jvonk/MIDImike/media/arduino.Still001.jpg

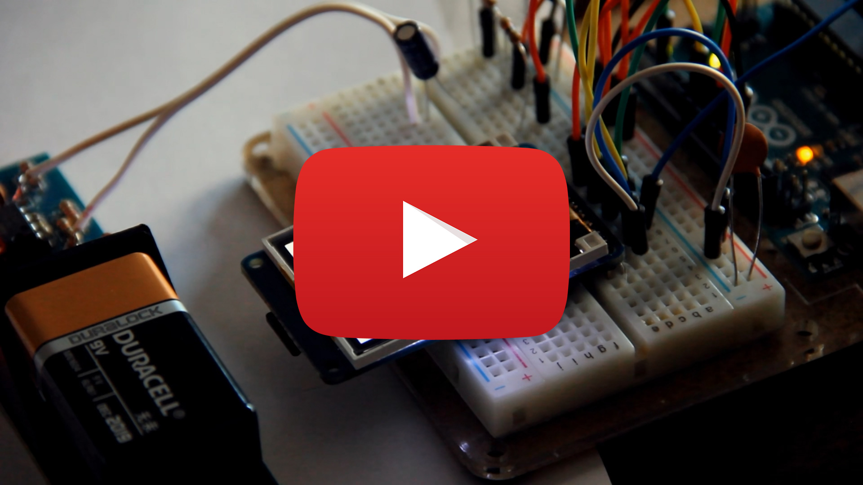
media/arduino.Still001.jpg
