jvonk/MIDImike/validation/N=200, S=9615, piano, interpolation.png

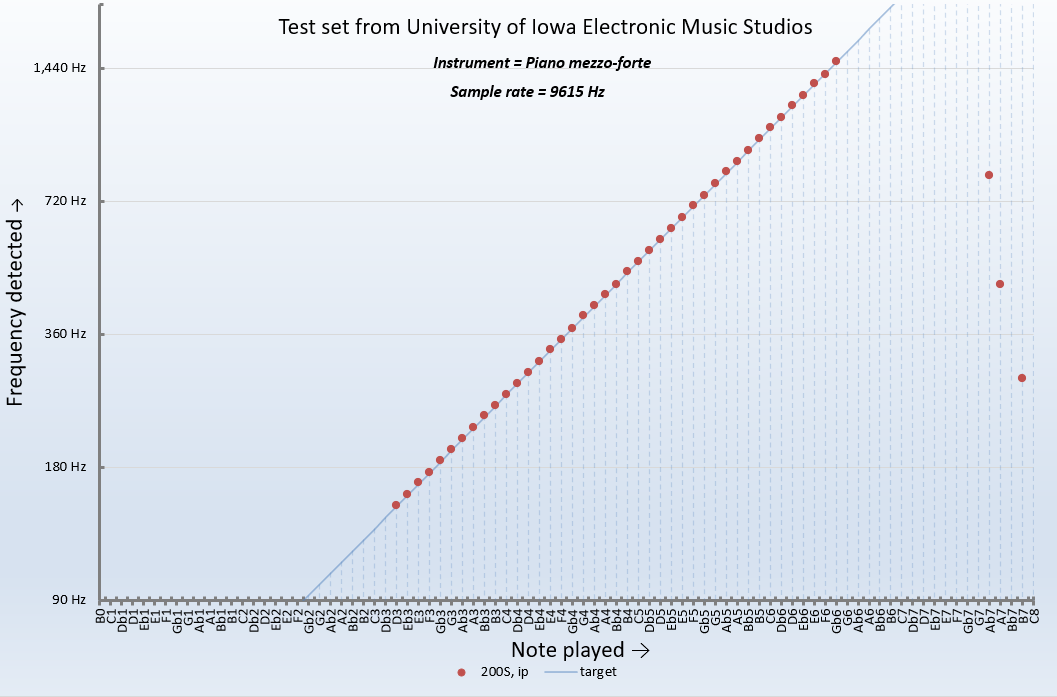
validation/N=200, S=9615, piano, interpolation.png
