jvonk/MIDImike/main/src/pitch/frequency.cpp

/**
 * @brief Frequency detector, using auto correlation to find frequency (f0) in signal
 * 
 * © Copyright 2015-2016,2022 Johan Vonk
 * 
 * This file is part of Arduino_pitch-detector.
 * 
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
 * SPDX-License-Identifier: GPL-3.0-or-later
 * SPDX-FileCopyrightText: Copyright 2015-2016,2022 Johan Vonk
 **/

#include <Arduino.h>
#include <stdint.h>
#include <limits.h>
#include "../../config.h"
#include "../../mapping.h"
#include "../microphone/microphone.h"
#include "frequency.h"

#define INTERPOLATE (1)
#define NORMALIZE (1)
#define DEBUG (0)

namespace  {
    typedef enum state_t {
        STATE_FIND_POS_SLOPE = 0,
        STATE_FIND_NEG_SLOPE,
        STATE_FOUND_PEAK,
    } state_t;

    typedef sample_cnt_t samplesLag_t;
    typedef int32_t autoCorr_t;
}

// calculate auto correlation for "lag"

static INLINE autoCorr_t
_cal_autocorrelation(samples_t const    samples,  // pointer to signed 8-bit data samples
  		             samplesLag_t const lag)      // lag
{
	// samples[ii] * samples[ii+lag], results in an int16 term
	// sum += term, results in an int32
	// To keep the sum to an int16, each time the term could be divided by nrOfSamples.
	//   to make the division faster, I would round nrOfSamples up to a 2^n boundary. (2BD)

	autoCorr_t ac = 0;

	for (sample_cnt_t ii = 0; ii < CONFIG_MIDIMIKE_WINDOW_SIZE - lag; ii++) {

		ac += ((int16_t)samples[ii] * samples[ii + lag]);
	}
	return ac;
}

static INLINE float                             // returns interpolated peak adjustment compared to peak location
_cal_interpolation_adj(autoCorr_t const left,   // sample value left of the peak
			           autoCorr_t const mid,    // sample value at the peak
			           autoCorr_t const right)  // sample value right of the peak
{
	float const adj = (float)0.5 * (right - left) / (2 * mid - left - right);
	return adj;
}

    /*********************
     * frequency_calculate
     *********************/

frequency_t                                    // returns frequency found, 0 when not found [out]
frequency_calculate(samples_t const  samples)  // pointer to signed 8-bit data samples [in]
{
	if (!samples) {
		return 0;
	}

#if 0
    for (size_t ii = 0; ii < CONFIG_MIDIMIKE_WINDOW_SIZE; ii++ ) {
        Serial.print(samples[ii]); Serial.print(" ");
    }
    Serial.println();
#endif

	float period = 0;
	autoCorr_t const acMax = _cal_autocorrelation(samples, 0);
	autoCorr_t const acThreshold = (float)acMax * (NORMALIZE ? (float)4/5 : (float)2/3);

    if (DEBUG) {
        Serial.print("acMax = "); Serial.print(acMax); 
        Serial.print(", acThreshold = "); Serial.println(acThreshold); 
    }
	autoCorr_t acPrev = acMax;
	state_t state = STATE_FIND_POS_SLOPE;   // ensure C++11 is enabled

	for (samplesLag_t lag = CONFIG_MIDIMIKE_LAG_MIN;
 		 (lag < CONFIG_MIDIMIKE_LAG_MAX) && (state != STATE_FOUND_PEAK); lag++) {

		autoCorr_t ac = _cal_autocorrelation(samples, lag);

        if (DEBUG) {
            Serial.print("k="); Serial.print(lag); Serial.print(": ac = "); Serial.println(ac);
        }

		if (NORMALIZE) {  // normalize for introduced zeros			
			ac = (float)ac * (float)CONFIG_MIDIMIKE_WINDOW_SIZE / (float)(CONFIG_MIDIMIKE_WINDOW_SIZE - lag);
		}

		// find peak after the initial maximum
		switch (state) {
			case STATE_FIND_POS_SLOPE:
				if ((ac > acThreshold) && (ac > acPrev)) {
					state = STATE_FIND_NEG_SLOPE;
				}
				break;
			case STATE_FIND_NEG_SLOPE:
				if (ac <= acPrev) {
					state = STATE_FOUND_PEAK;
					if (INTERPOLATE) {
						period = lag - 1 + _cal_interpolation_adj(
							_cal_autocorrelation(samples, lag - 2), 
							acPrev, ac);
					} else {
						period = lag - 1;  // we got 1 past it
					}
				}
				break;
            case STATE_FOUND_PEAK:
                break;
		}
		acPrev = ac;
	}

	if (state != STATE_FOUND_PEAK) {
		return 0;
	}

	frequency_t const f = (float)CONFIG_MIDIMIKE_SAMPLE_RATE / period;

    if (DEBUG) {
        Serial.print("freq = "); Serial.print(f);
        Serial.print(", max = "); Serial.println(CONFIG_MIDIMIKE_FREQ_MAX);
    }
	bool const ok = f < CONFIG_MIDIMIKE_FREQ_MAX;
	return ok ? f : 0;
}
