jvonk/MIDImike/main/src/sdcard/sddir.cpp

/**
 * @brief Iterate through files on SD card
 * 
 * Note: the functions themselves are non-reentrant
 *
 * © Copyright 2015-2016,2022 Johan Vonk
 * 
 * This file is part of Arduino_pitch-detector.
 * 
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
 * SPDX-License-Identifier: GPL-3.0-or-later
 * SPDX-FileCopyrightText: Copyright 2015-2016,2022 Johan Vonk
 **/

#include <Arduino.h>
#include <stdint.h>
#include <SdFat.h>

#include "../../config.h"
#include "../debug/debug.h"
#include "sddir.h"

#define SD_FAT_TYPE (1) // FAT16/32
#if USB == USB_SERIAL
#  define error(s) sd.errorHalt(&Serial, F(s));
#else
#  define error(s) 
#endif

namespace {
    SdFat sd;
}


    /************
     * initialize
     ************/

uint_least8_t                           // returns 0 if successful, otherwise returns 1
sddir_init(uint_least8_t const cs_pin)  // GPIO# used for SD Chip Select pin
{
	return !sd.begin(cs_pin);
}

#if (SRC == SRC_FILE)

// maximum level of sub directories to search
#define DIRLEVEL_MAX (2)

    /****************************
     * recursively walk directory
     ****************************/ 

static uint_least8_t                     // returns 0 if successful
_walkDirectory(File & dir,               // directory to start at
               uint_least8_t const lvl,  // current level
               sddir_callback_t cb_fnc)  // function to call for each file
{
	uint_least8_t err = 0;
	static char instrumentName[8 + 1 + 3 + 1];

    File file;
    while (file.openNext(&dir, O_RDONLY)) {
        if (file.isDir()) {
			if (lvl < DIRLEVEL_MAX) {
				if (lvl == 0) {
                    file.getName8(instrumentName, sizeof(instrumentName));
                    //Serial.println(instrumentName);
				}
				err = _walkDirectory(file, lvl + 1, cb_fnc);  // recursive function call
            }
        } else {            
			err = (*cb_fnc)(file, instrumentName);  // call back registered function
        }
        file.close();
    }
	return err;
}

    /****************************
     * for each file in directory
     **************************** 
     * Problems?  Try using a >= 2G formatted as FAT using https://www.sdcard.org/downloads/formatter/
     */

uint_least8_t                                           // returns 0 if successful
sddir_for_each_file_in_dir(char const * const dirName,  // directory (and its sub directories) to search
                           sddir_callback_t cb_fnc)     // function to call for each file found
{
    File dir;

    if (!dir.open(dirName)){
        error("dir.open failed");
    }

	uint_least8_t err = _walkDirectory(dir, 0, cb_fnc);

	dir.close();
	return err;
}

#endif
