jvonk/MIDImike/main/mapping.h

#pragma once

#define INLINE inline
#define ALWAYS_INLINE __attribute__((always_inline))
#define STATIC static

#define ALIGN( type ) __attribute__((aligned( __alignof__( type ) )))
#define PACK( type )  __attribute__((aligned( __alignof__( type ) ), packed ))
#define PACK8  __attribute__((aligned( __alignof__( uint8_t ) ), packed ))

#ifndef ARRAY_SIZE
# define ARRAY_SIZE(a) (sizeof(a) / sizeof(*(a)))
#endif
